jotego/jt49/hdl/jt49.v

/*  This file is part of JT49.

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
    Author: Jose Tejada Gomez. Twitter: @topapate
    Version: 1.0
    Date: 10-Nov-2018

    Based on sqmusic, by the same author

    */
/* verilator coverage_off */
module jt49 ( // note that input ports are not multiplexed
    input            rst_n,
    input            clk,    // signal on positive edge
    input            clk_en /* synthesis direct_enable = 1 */,
    input  [3:0]     addr,
    input            cs_n,
    input            wr_n,  // write
    input  [7:0]     din,
    input            sel, // if sel is low, the clock is divided by 2
    output reg [7:0] dout,
    output reg [9:0] sound,  // combined channel output
    output reg [7:0] A,      // linearised channel output
    output reg [7:0] B,
    output reg [7:0] C,
    output           sample,

    input      [7:0] IOA_in,
    output     [7:0] IOA_out,
    output           IOA_oe,

    input      [7:0] IOB_in,
    output     [7:0] IOB_out,
    output           IOB_oe
);

parameter [2:0] COMP=3'b000;
parameter       YM2203_LUMPED=0;
parameter       CLKDIV=3;
wire [2:0] comp = COMP;

reg  [ 7:0] regarray[15:0];
wire [ 7:0] port_A, port_B;
wire [11:0] periodA, periodB, periodC;

wire [4:0] envelope;
wire bitA, bitB, bitC;
wire noise;
reg Amix, Bmix, Cmix;

wire cen16, cen256;

assign IOA_out = regarray[14];
assign IOB_out = regarray[15];
assign port_A  = IOA_in;
assign port_B  = IOB_in;
assign IOA_oe  = regarray[7][6];
assign IOB_oe  = regarray[7][7];
assign sample  = cen16;
assign periodA = { regarray[1][3:0], regarray[0][7:0] };
assign periodB = { regarray[3][3:0], regarray[2][7:0] };
assign periodC = { regarray[5][3:0], regarray[4][7:0] };


jt49_cen #(.CLKDIV(CLKDIV)) u_cen(
    .clk    ( clk     ),
    .rst_n  ( rst_n   ),
    .cen    ( clk_en  ),
    .sel    ( sel     ),
    .cen16  ( cen16   ),
    .cen256 ( cen256  )
);

// internal modules operate at clk/16
jt49_div #(12) u_chA(
    .clk        ( clk           ),
    .rst_n      ( rst_n         ),
    .cen        ( cen16         ),
    .period     ( periodA       ),
    .div        ( bitA          )
);

jt49_div #(12) u_chB(
    .clk        ( clk           ),
    .rst_n      ( rst_n         ),
    .cen        ( cen16         ),
    .period     ( periodB       ),
    .div        ( bitB          )
);

jt49_div #(12) u_chC(
    .clk        ( clk           ),
    .rst_n      ( rst_n         ),
    .cen        ( cen16         ),
    .period     ( periodC       ),
    .div        ( bitC          )
);

jt49_noise u_ng(
    .clk    ( clk               ),
    .cen    ( cen16             ),
    .rst_n  ( rst_n             ),
    .period ( regarray[6][4:0]  ),
    .noise  ( noise             )
);

// envelope generator
wire eg_step;
wire [15:0] eg_period   = {regarray[4'hc],regarray[4'hb]};
wire        null_period = eg_period == 16'h0;

jt49_div #(16) u_envdiv(
    .clk    ( clk               ),
    .cen    ( cen256            ),
    .rst_n  ( rst_n             ),
    .period ( eg_period         ),
    .div    ( eg_step           )
);

reg eg_restart;

jt49_eg u_env(
    .clk        ( clk               ),
    .cen        ( cen256            ),
    .step       ( eg_step           ),
    .rst_n      ( rst_n             ),
    .restart    ( eg_restart        ),
    .null_period( null_period       ),
    .ctrl       ( regarray[4'hD][3:0] ),
    .env        ( envelope          )
);

reg  [4:0] logA, logB, logC, log;
wire [7:0] lin;

jt49_exp u_exp(
    .clk    ( clk  ),
    .comp   ( comp ),
    .din    ( log  ),
    .dout   ( lin  )
);

wire [4:0] volA = { regarray[ 8][3:0], regarray[ 8][3] };
wire [4:0] volB = { regarray[ 9][3:0], regarray[ 9][3] };
wire [4:0] volC = { regarray[10][3:0], regarray[10][3] };
wire use_envA = regarray[ 8][4];
wire use_envB = regarray[ 9][4];
wire use_envC = regarray[10][4];
wire use_noA  = regarray[ 7][3];
wire use_noB  = regarray[ 7][4];
wire use_noC  = regarray[ 7][5];

reg [3:0] acc_st;

always @(posedge clk) if( clk_en ) begin
    Amix <= (noise|use_noA) & (bitA|regarray[7][0]);
    Bmix <= (noise|use_noB) & (bitB|regarray[7][1]);
    Cmix <= (noise|use_noC) & (bitC|regarray[7][2]);

    logA <= !Amix ? 5'd0 : (use_envA ? envelope : volA );
    logB <= !Bmix ? 5'd0 : (use_envB ? envelope : volB );
    logC <= !Cmix ? 5'd0 : (use_envC ? envelope : volC );
end

reg  [9:0] acc;
wire [9:0] elin;

assign elin = {2'd0,lin};

always @(posedge clk, negedge rst_n) begin
    if( !rst_n ) begin
        acc_st <= 4'b1;
        acc    <= 10'd0;
        A      <= 8'd0;
        B      <= 8'd0;
        C      <= 8'd0;
        sound  <= 10'd0;
    end else if(clk_en) begin
        acc_st <= { acc_st[2:0], acc_st[3] };
        // Lumping the channel outputs for YM2203 will cause only the higher
        // voltage to pass throuh, as the outputs seem to use a source follower.
        acc    <= YM2203_LUMPED==1 ? (acc>elin ? acc : elin) : acc + elin;
        case( acc_st )
            4'b0001: begin
                log   <= logA;
                acc   <= 10'd0;
                sound <= acc;
            end
            4'b0010: begin
                A   <= lin;
                log <= logB;
            end
            4'b0100: begin
                B   <= lin;
                log <= logC;
            end
            4'b1000: begin // last sum
                C   <= lin;
            end
            default:;
        endcase
    end
end

reg  [7:0] read_mask;

always @(*)
    case(addr)
        4'h0,4'h2,4'h4,4'h7,4'hb,4'hc,4'he,4'hf:
            read_mask = 8'hff;
        4'h1,4'h3,4'h5,4'hd:
            read_mask = 8'h0f;
        4'h6,4'h8,4'h9,4'ha:
            read_mask = 8'h1f;
    endcase // addr

// register array
wire write;
reg  last_write;
wire wr_edge = write & ~last_write;

assign write = !wr_n && !cs_n;

always @(posedge clk, negedge rst_n) begin
    if( !rst_n ) begin
        dout       <= 8'd0;
        last_write <= 0;
        eg_restart <= 0;
        regarray[0]<=8'd0; regarray[4]<=8'd0; regarray[ 8]<=8'd0; regarray[12]<=8'd0;
        regarray[1]<=8'd0; regarray[5]<=8'd0; regarray[ 9]<=8'd0; regarray[13]<=8'd0;
        regarray[2]<=8'd0; regarray[6]<=8'd0; regarray[10]<=8'd0; regarray[14]<=8'd0;
        regarray[3]<=8'd0; regarray[7]<=8'd0; regarray[11]<=8'd0; regarray[15]<=8'd0;
    end else begin
        last_write  <= write;
        // Data read
        case( addr )
            4'he: dout <= port_A;
            4'hf: dout <= port_B;
            default: dout <= regarray[ addr ] & read_mask;
        endcase
        // Data write
        if( write ) begin
            regarray[addr] <= din;
            if ( addr == 4'hD && wr_edge ) eg_restart <= 1;
        end else begin
            eg_restart <= 0;
        end
    end
end

endmodule
