jotego/jt49/hdl/jt49_exp.v

/*  This file is part of JT49.

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
    Author: Jose Tejada Gomez. Twitter: @topapate
    Version: 1.0
    Date: 10-Nov-2018
    
    Based on sqmusic, by the same author
    
    */

// Compression vs dynamic range
// 0 -> 43.6dB
// 1 -> 29.1
// 2 -> 21.8
// 3 -> 13.4
/* verilator coverage_off */
module jt49_exp(
    input            clk,
    input      [2:0] comp,  // compression
    input      [4:0] din,
    output reg [7:0] dout 
);

reg [7:0] lut[0:159];

always @(posedge clk)
    dout <= lut[ {comp,din} ];

initial begin
    lut[0] = 8'd0;
    lut[1] = 8'd1;
    lut[2] = 8'd1;
    lut[3] = 8'd1;
    lut[4] = 8'd2;
    lut[5] = 8'd2;
    lut[6] = 8'd3;
    lut[7] = 8'd3;
    lut[8] = 8'd4;
    lut[9] = 8'd5;
    lut[10] = 8'd6;
    lut[11] = 8'd7;
    lut[12] = 8'd9;
    lut[13] = 8'd11;
    lut[14] = 8'd13;
    lut[15] = 8'd15;
    lut[16] = 8'd18;
    lut[17] = 8'd22;
    lut[18] = 8'd26;
    lut[19] = 8'd31;
    lut[20] = 8'd37;
    lut[21] = 8'd45;
    lut[22] = 8'd53;
    lut[23] = 8'd63;
    lut[24] = 8'd75;
    lut[25] = 8'd90;
    lut[26] = 8'd107;
    lut[27] = 8'd127;
    lut[28] = 8'd151;
    lut[29] = 8'd180;
    lut[30] = 8'd214;
    lut[31] = 8'd255;
    lut[32] = 8'd0;
    lut[33] = 8'd7;
    lut[34] = 8'd8;
    lut[35] = 8'd10;
    lut[36] = 8'd11;
    lut[37] = 8'd12;
    lut[38] = 8'd14;
    lut[39] = 8'd15;
    lut[40] = 8'd17;
    lut[41] = 8'd20;
    lut[42] = 8'd22;
    lut[43] = 8'd25;
    lut[44] = 8'd28;
    lut[45] = 8'd31;
    lut[46] = 8'd35;
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
    lut[148] = 8'd141;
    lut[149] = 8'd149;
    lut[150] = 8'd157;
    lut[151] = 8'd166;
    lut[152] = 8'd175;
    lut[153] = 8'd185;
    lut[154] = 8'd195;
    lut[155] = 8'd206;
    lut[156] = 8'd217;
    lut[157] = 8'd229;
    lut[158] = 8'd241;
    lut[159] = 8'd255;

end
endmodule
